chirimen-oh/Cases/kimono/img/05.jpg

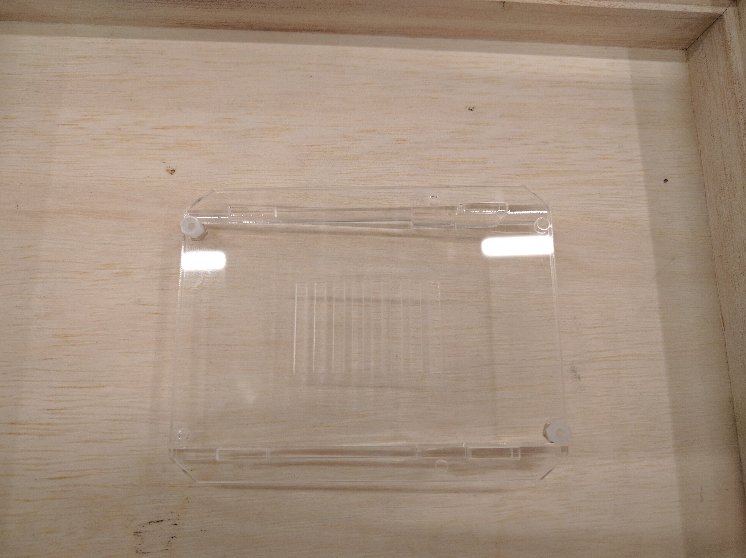
kimono/img/05.jpg
