chirimen-oh/Cases/kimono/img/06.jpg

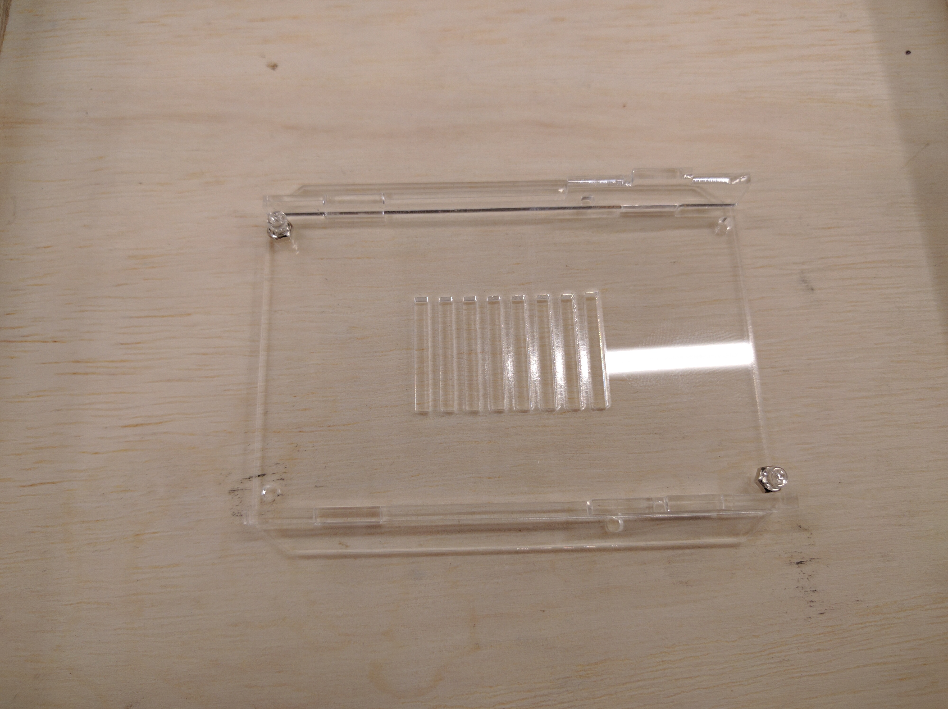
kimono/img/06.jpg
